hack-apollo/hack_amp/Images/2.PNG

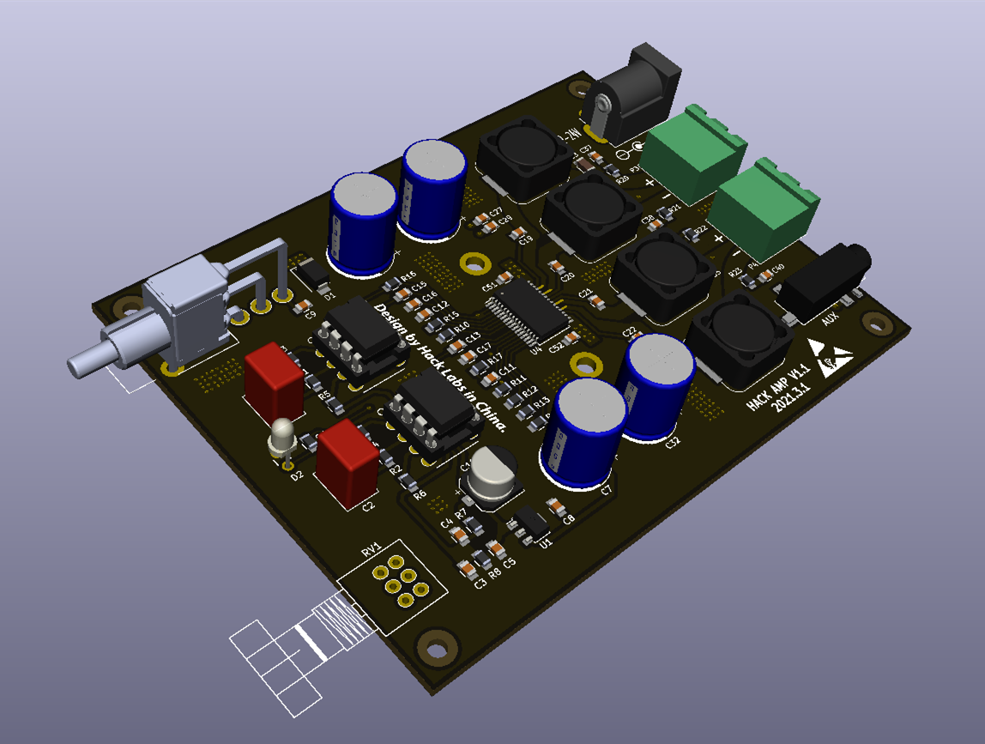
Images/2.PNG
